BrandonFors/convention_pcb_badge/badge_code/devkitc-3/components/epaper/include/imgs.h

#ifndef IMGS_H
#define IMGS_H

extern const unsigned char irishsat_bitmap[];
extern const unsigned char gImage[];
extern const unsigned char epd_bitmap_Nametag[];
extern const unsigned char epd_bitmap_website[];
extern const unsigned char epd_bitmap_opensauce[];

#endif
