BrandonFors/convention_pcb_badge/badge_code/devkitc-3/components/esp32_hal/hal.h

#ifndef HAL_H
#define HAL_H
#include <stdint.h>

typedef enum {
    HAL_GPIO_LOW = 0,
    HAL_GPIO_HIGH = 1
}hal_gpio_out_t;

#define SPI_SPEED 500000

void hal_init();

//General
void hal_delay_us(uint32_t us);
void hal_delay_ms(uint32_t ms);
uint64_t hal_get_time_ms();

//GPIO
void hal_gpio_set(uint8_t pin, hal_gpio_out_t output);
uint8_t hal_gpio_read(uint8_t pin);
void hal_gpio_register_callback(uint8_t pin, void *callback, void *args);

//SPI
void hal_spi_send_byte(uint8_t byte);

#endif /* HAL_H */
