BrandonFors/convention_pcb_badge/badge_code/devkitc-3/components/buttons/include/buttons.h

#ifndef BUTTONS_H
#define BUTTONS_H

#define DEBOUNCE_TIME_MS 250


typedef enum {
  BUTTON_1 = 1,
  BUTTON_2 = 2,
  BUTTON_3 = 3,
  NA = 4,
} ButtonEvent;

void slide_hold();
void slide_forward();
void slide_backward();

void buttons_init();

#endif
